MuffinByteLabs/esp32s3-plant-monitor/docs/images/Kicad/Screenshot 2026-09-09 122327.png

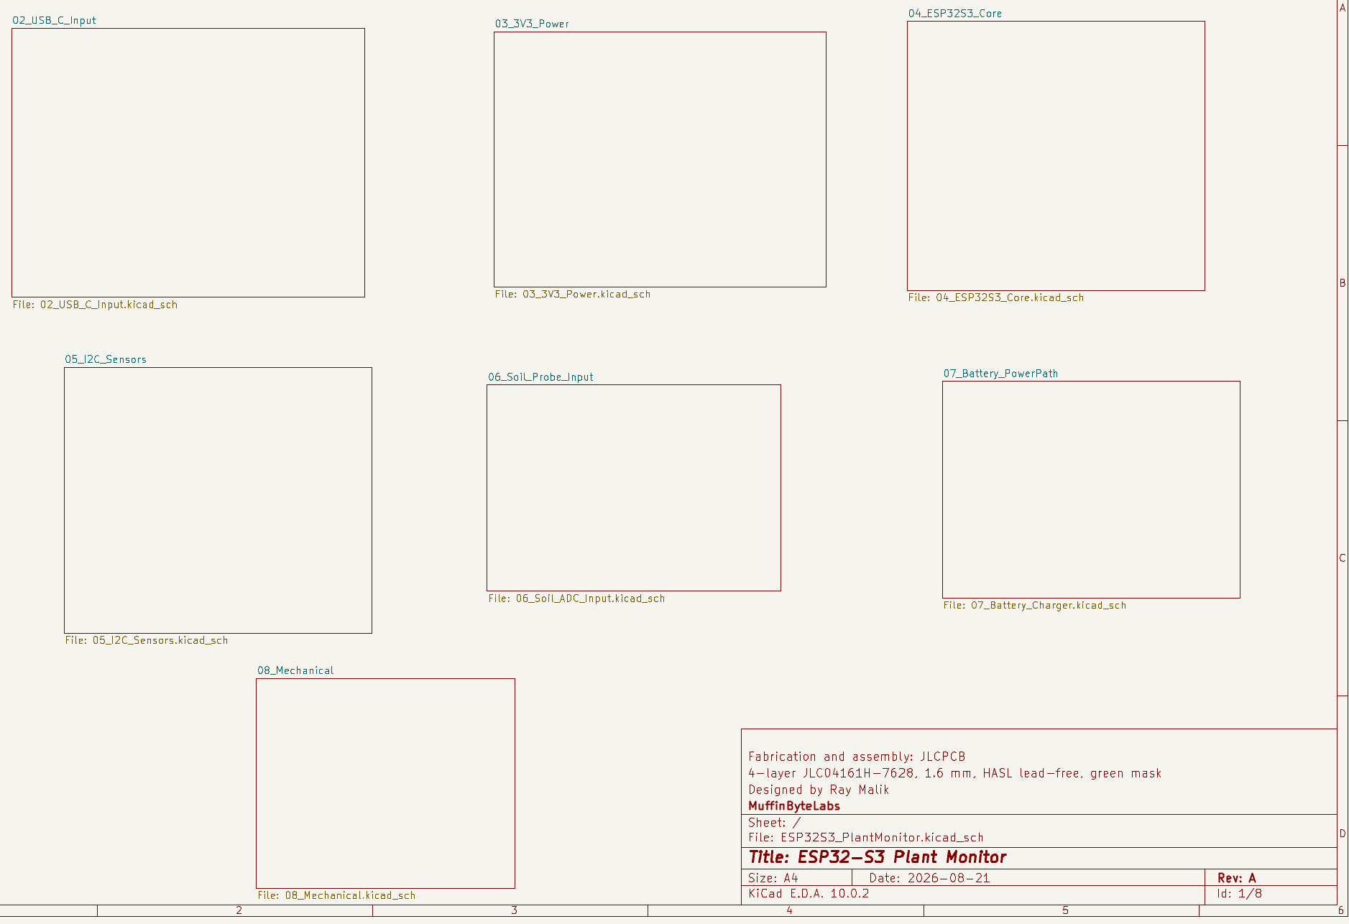
docs/images/Kicad/Screenshot 2026-09-09 122327.png
