MuffinByteLabs/esp32s3-plant-monitor/docs/images/Physical board/back.png

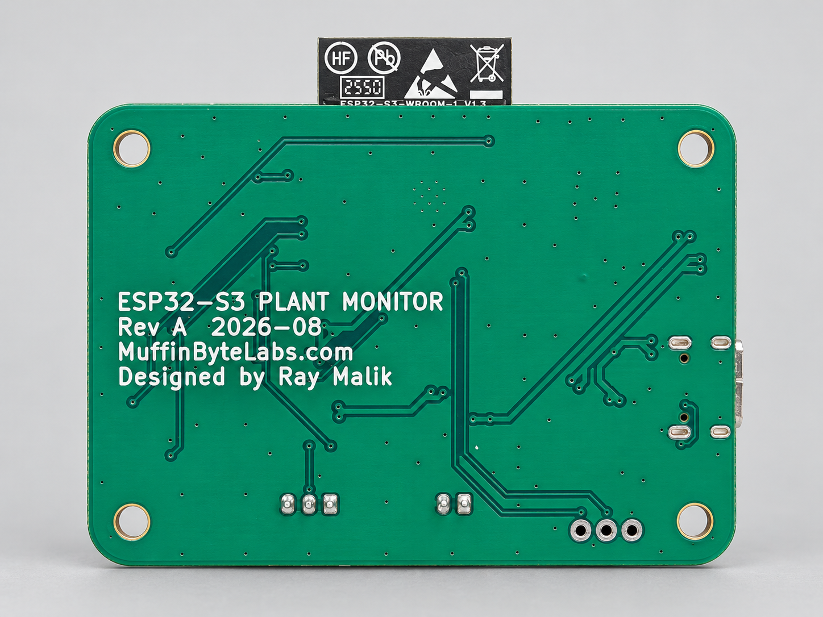
docs/images/Physical board/back.png
