MuffinByteLabs/esp32s3-plant-monitor/docs/reviews/Placement_Review_RevA_2026-08-10_map.png

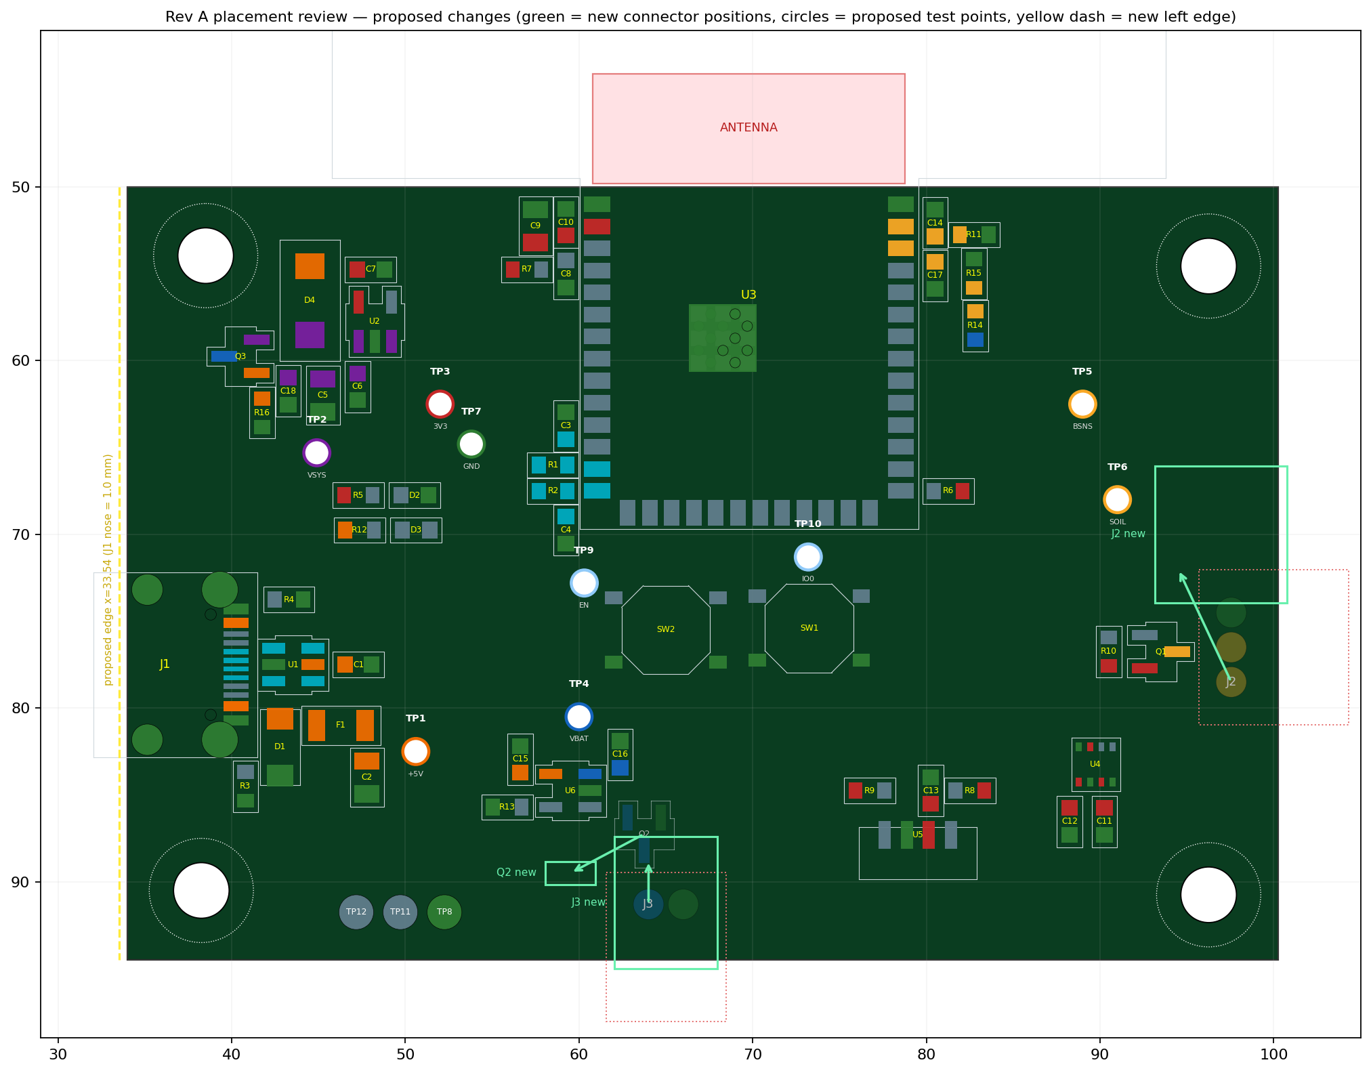
docs/reviews/Placement_Review_RevA_2026-08-10_map.png
