MuffinByteLabs/esp32s3-plant-monitor/fabrication/revA/production_check/4_order_number_removed.png

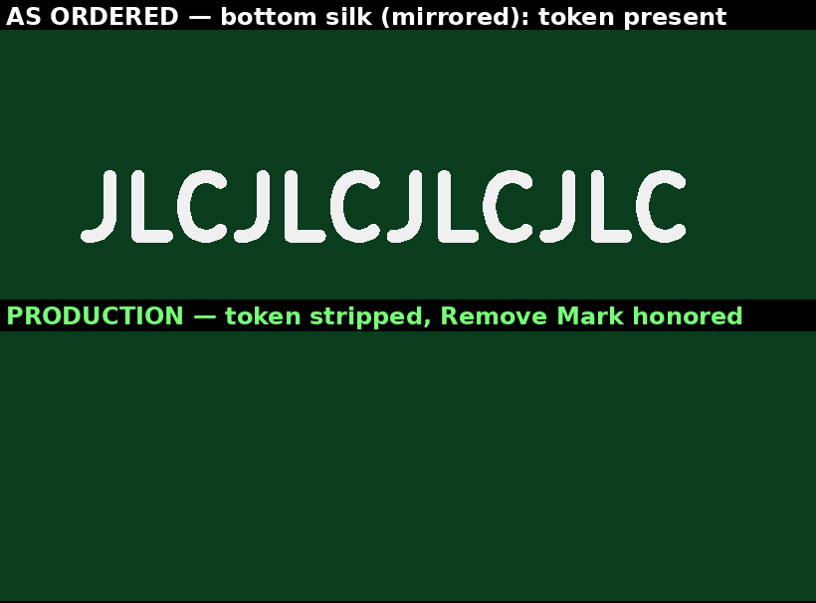
fabrication/revA/production_check/4_order_number_removed.png
