MuffinByteLabs/esp32s3-plant-monitor/fabrication/revA/production_check/2_antenna_over_rail.png

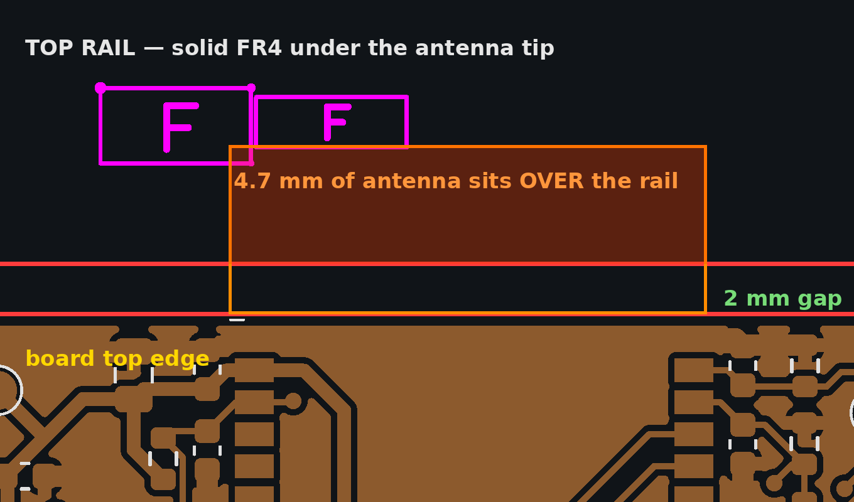
fabrication/revA/production_check/2_antenna_over_rail.png
