MuffinByteLabs/esp32s3-plant-monitor/fabrication/revA/production_check/3_usb_on_vcut_rail.png

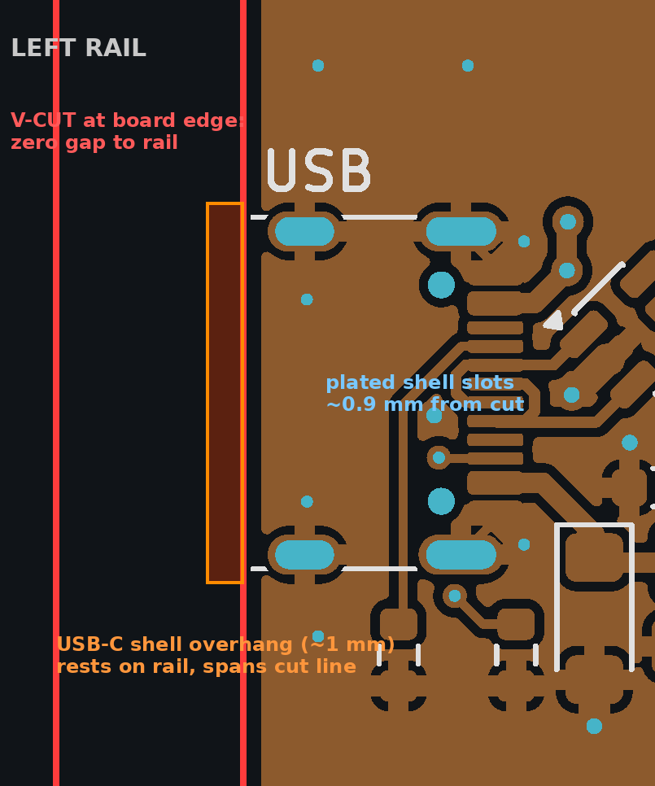
fabrication/revA/production_check/3_usb_on_vcut_rail.png
